hiveeyes/save-the-bees-esp8266-arduino/assets/02.png

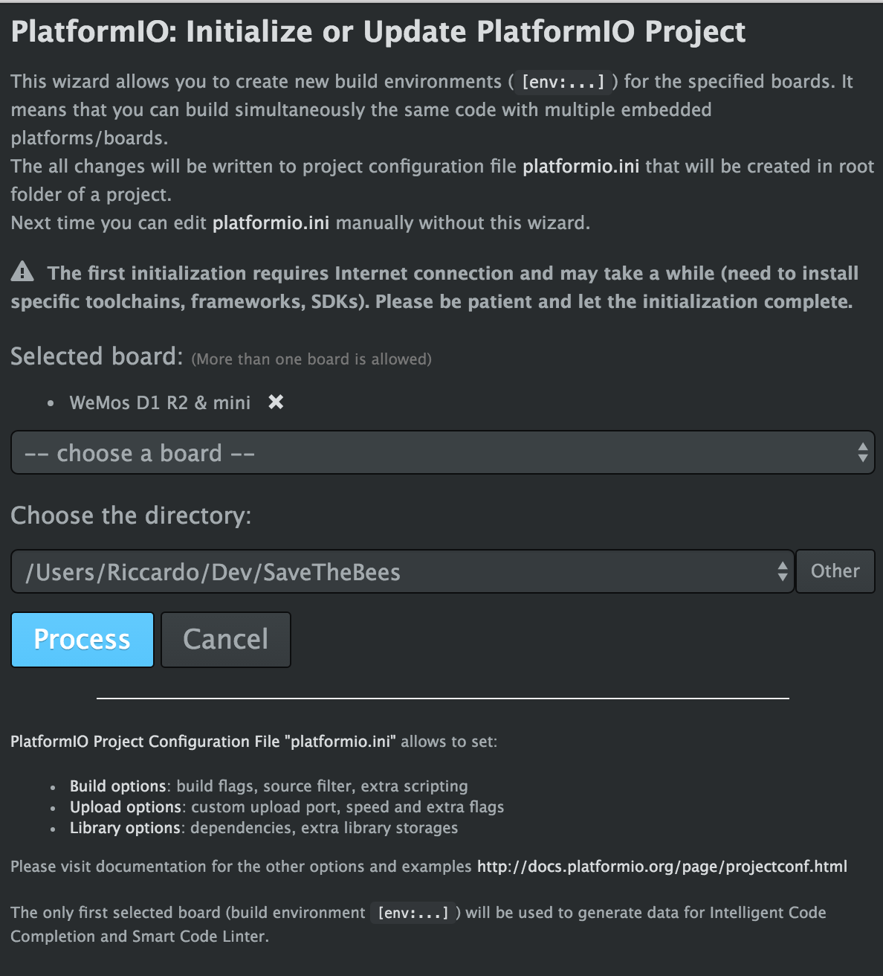
assets/02.png
