hiveeyes/save-the-bees-esp8266-arduino/assets/Platform.png

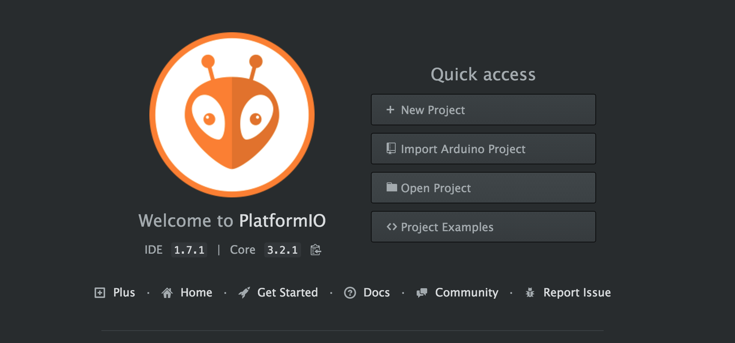
assets/Platform.png
