hiveeyes/save-the-bees-esp8266-arduino/assets/Schermata 2017-01-18 alle 18.19.47.png

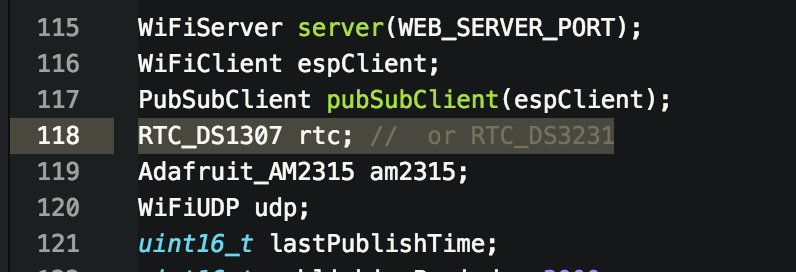
assets/Schermata 2017-01-18 alle 18.19.47.png
